hungrygeek/HSKB/case_customization/renders/hero2_sskb.png

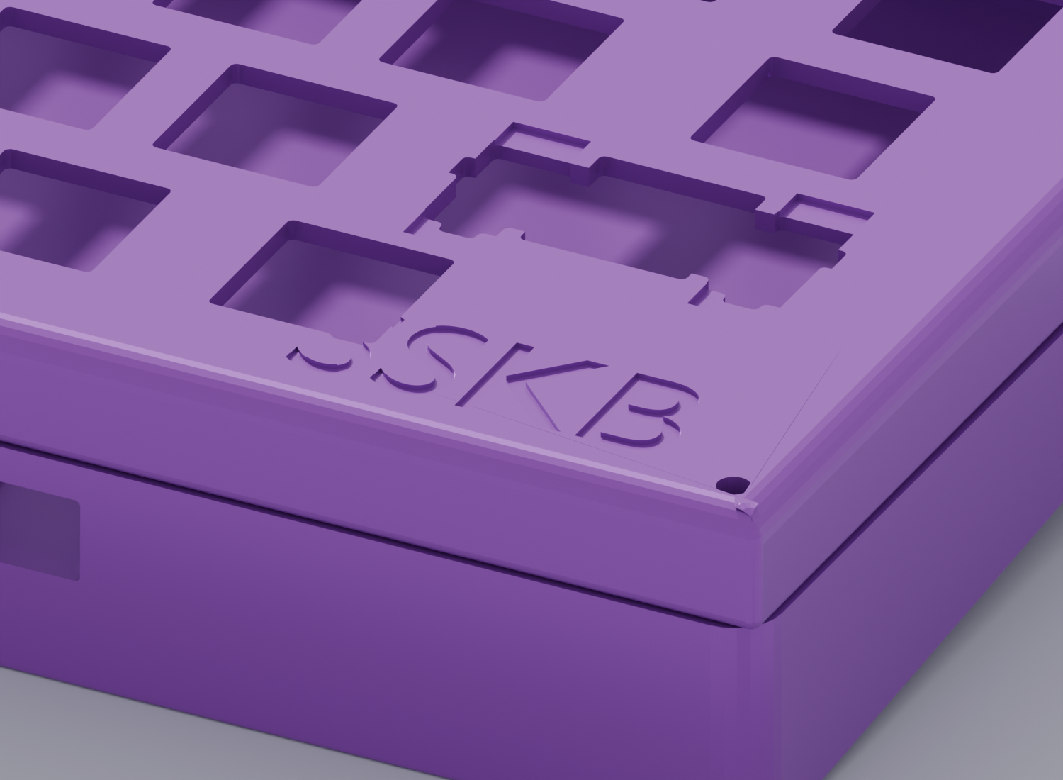
case_customization/renders/hero2_sskb.png
