hungrygeek/HSKB/case_customization/renders/hero3_sskb.png

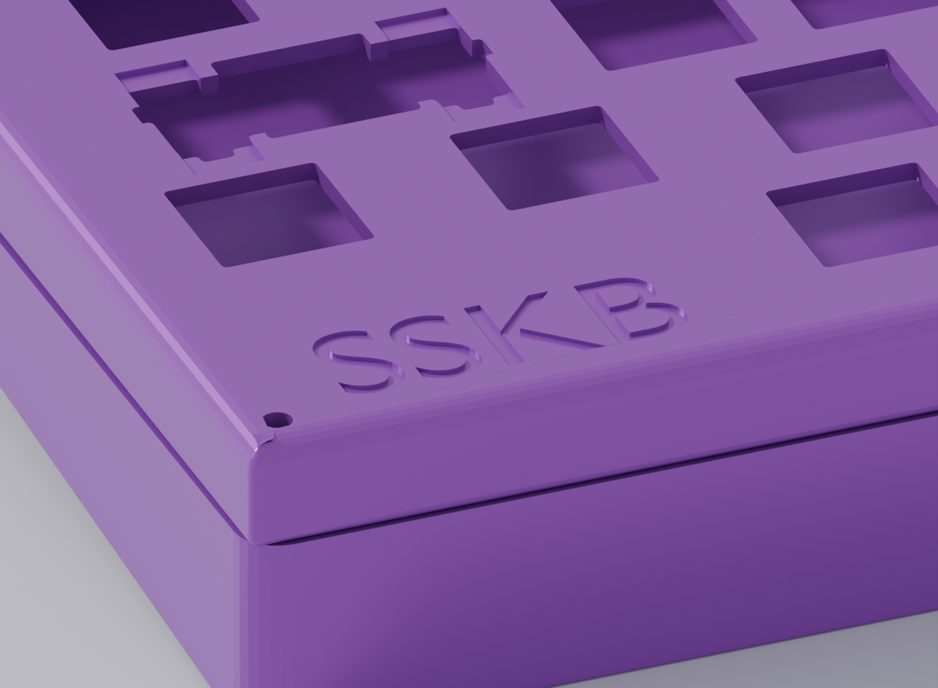
case_customization/renders/hero3_sskb.png
