hungrygeek/HSKB/case_customization/renders/after_15_corner.png

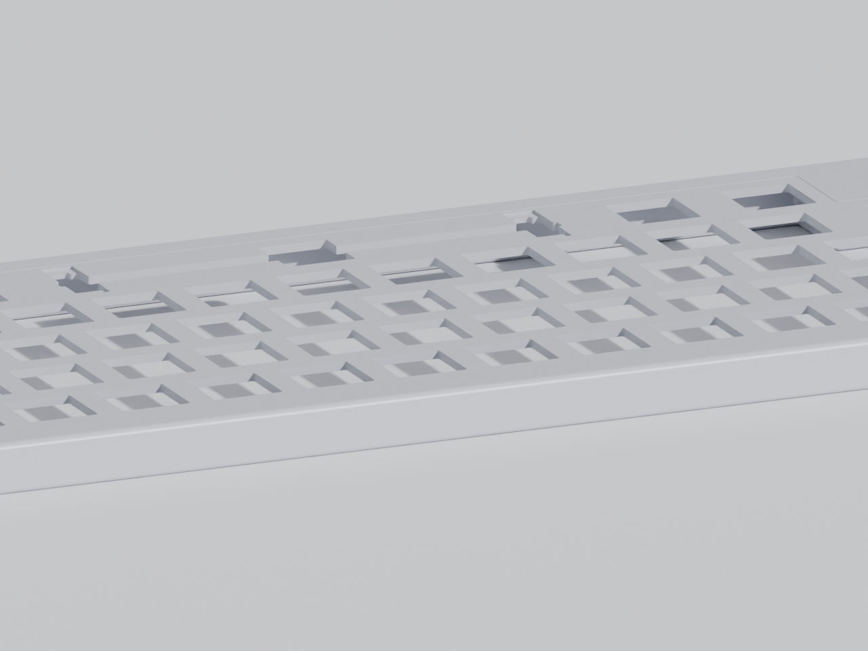
case_customization/renders/after_15_corner.png
