hungrygeek/HSKB/case_customization/renders/after_15_iso.png

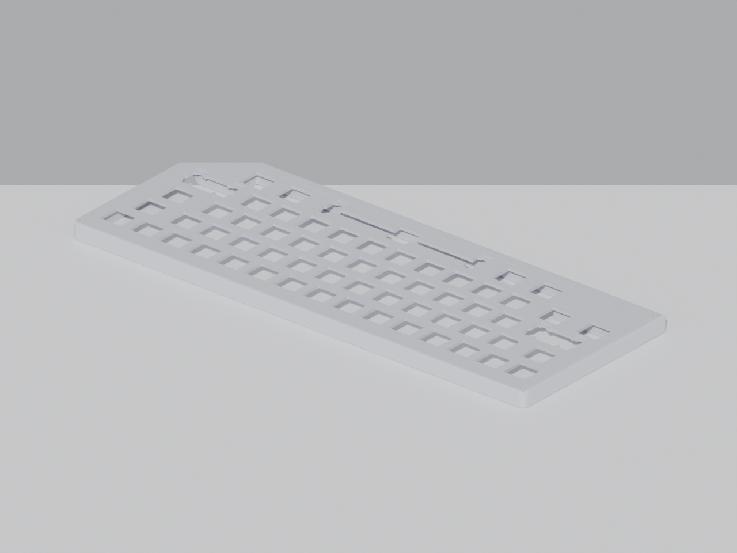
case_customization/renders/after_15_iso.png
