hungrygeek/HSKB/case_customization/renders/after_15_top.png

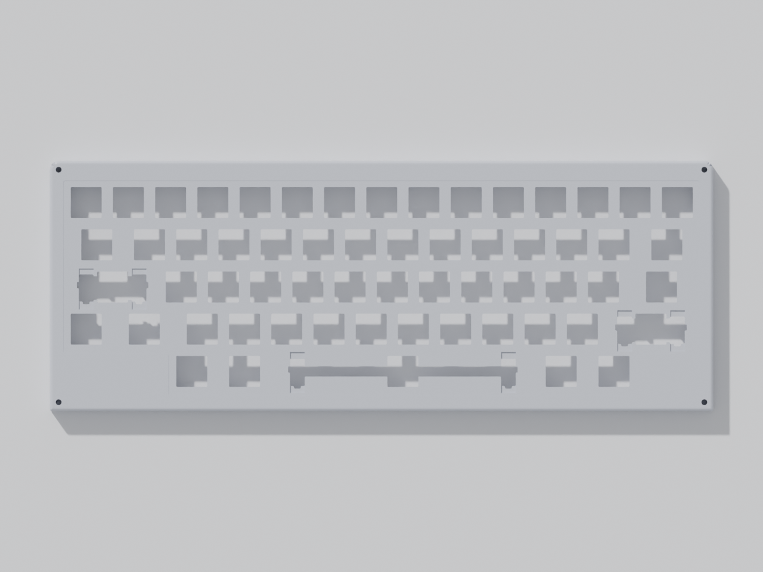
case_customization/renders/after_15_top.png
