hungrygeek/HSKB/case_customization/renders/bottom_before_corner.png

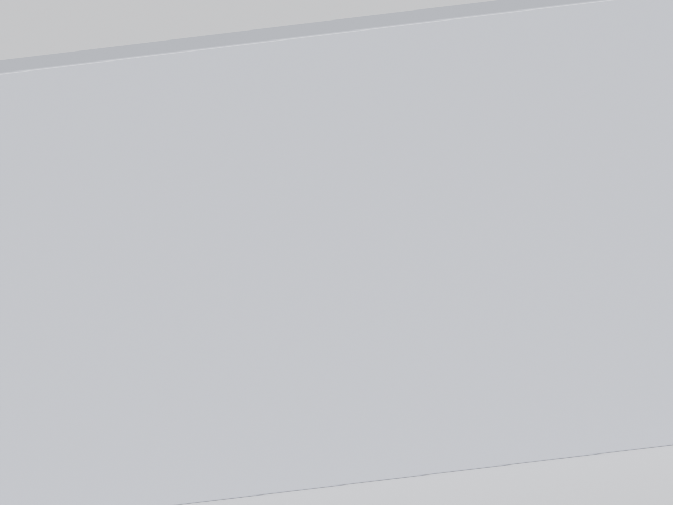
case_customization/renders/bottom_before_corner.png
