hungrygeek/HSKB/case_customization/renders/bottom_before_iso.png

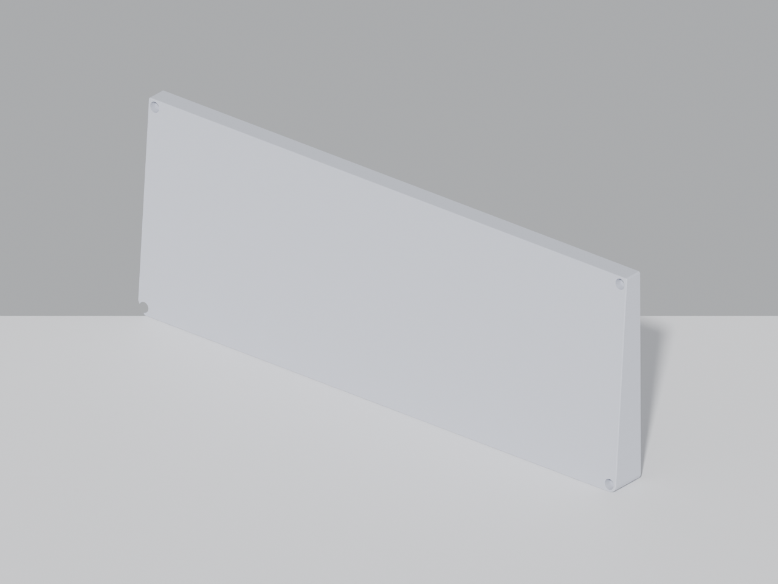
case_customization/renders/bottom_before_iso.png
