hungrygeek/HSKB/case_customization/renders/bottom_up_corner.png

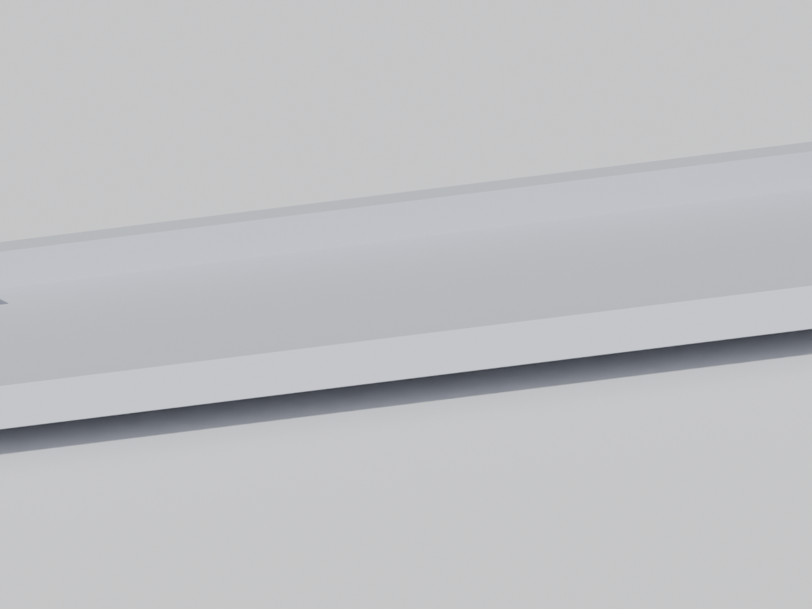
case_customization/renders/bottom_up_corner.png
