hungrygeek/HSKB/case_customization/renders/bottom_up_iso.png

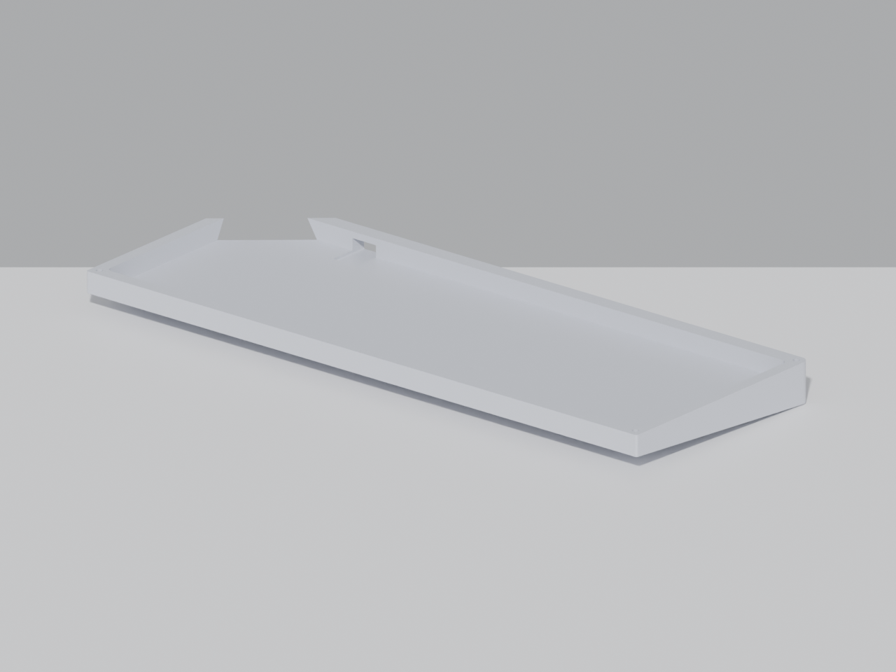
case_customization/renders/bottom_up_iso.png
