hungrygeek/HSKB/case_customization/renders/diag_frontright.png

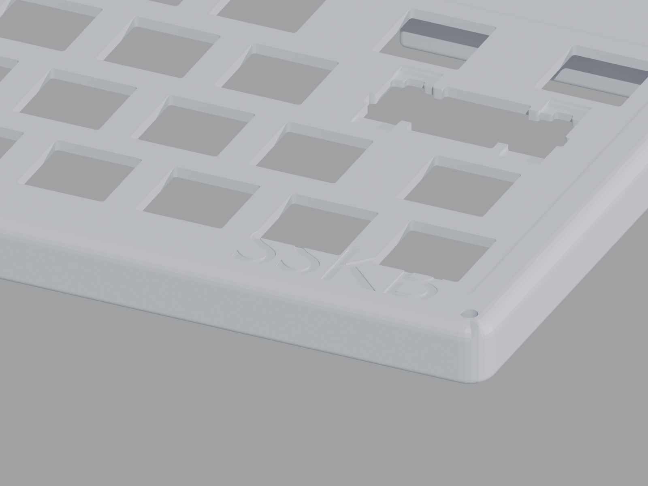
case_customization/renders/diag_frontright.png
