hungrygeek/HSKB/case_customization/renders/engrave2_angle.png

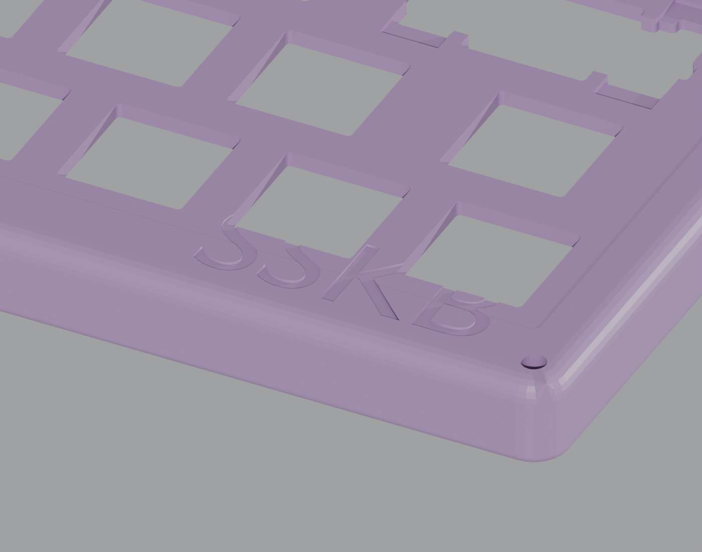
case_customization/renders/engrave2_angle.png
