hungrygeek/HSKB/case_customization/renders/engrave2_top.png

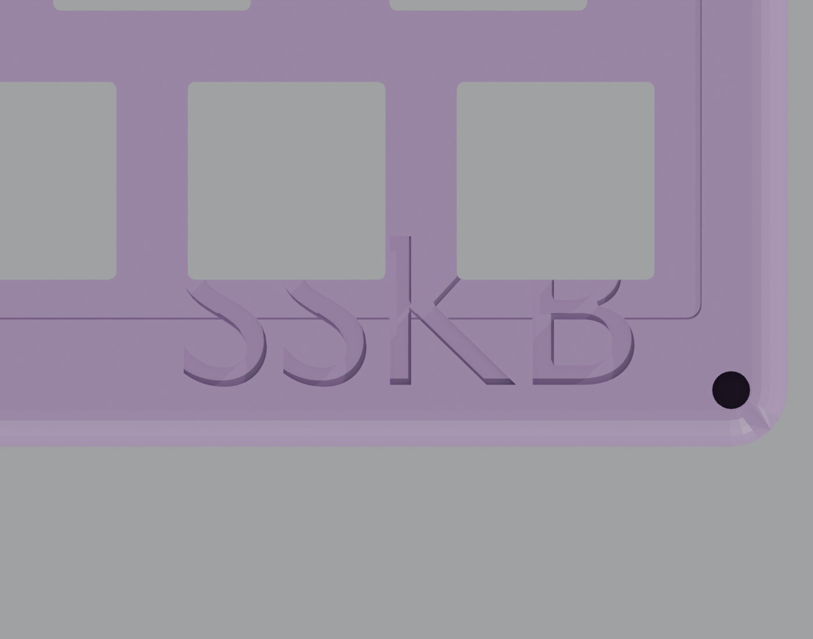
case_customization/renders/engrave2_top.png
