hungrygeek/HSKB/case_customization/renders/final_top_corner.png

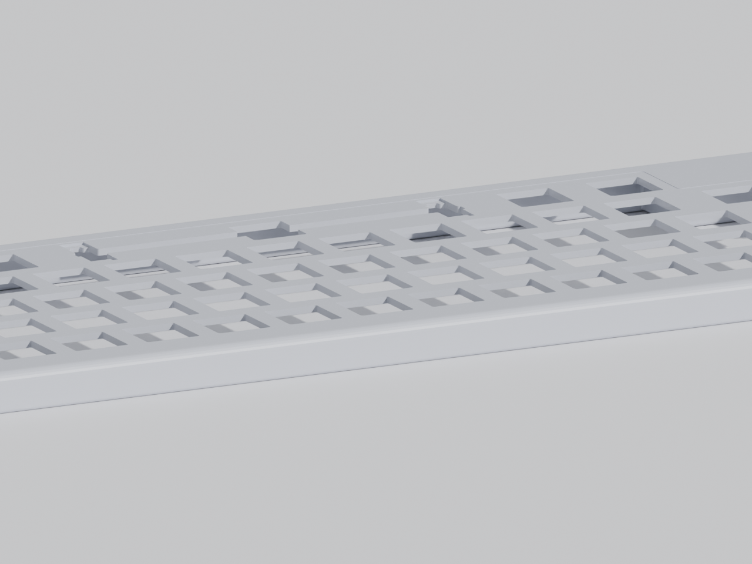
case_customization/renders/final_top_corner.png
