hungrygeek/HSKB/case_customization/renders/final_top_iso.png

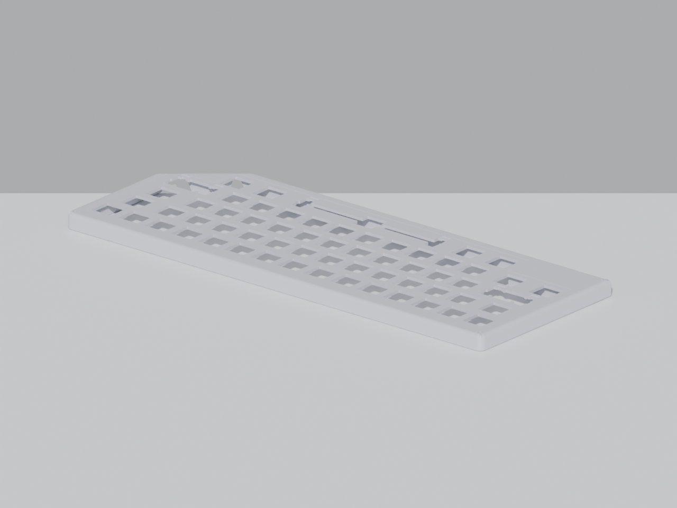
case_customization/renders/final_top_iso.png
