hungrygeek/HSKB/case_customization/renders/hero2_hero.png

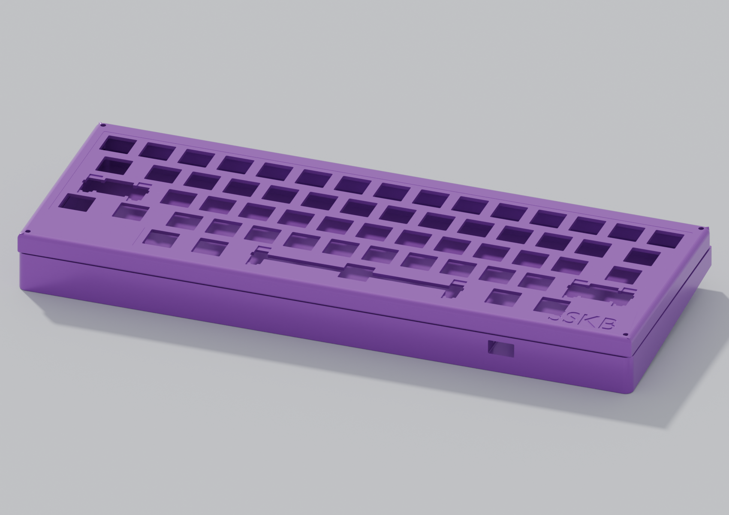
case_customization/renders/hero2_hero.png
