hungrygeek/HSKB/case_customization/renders/hero3_hero.png

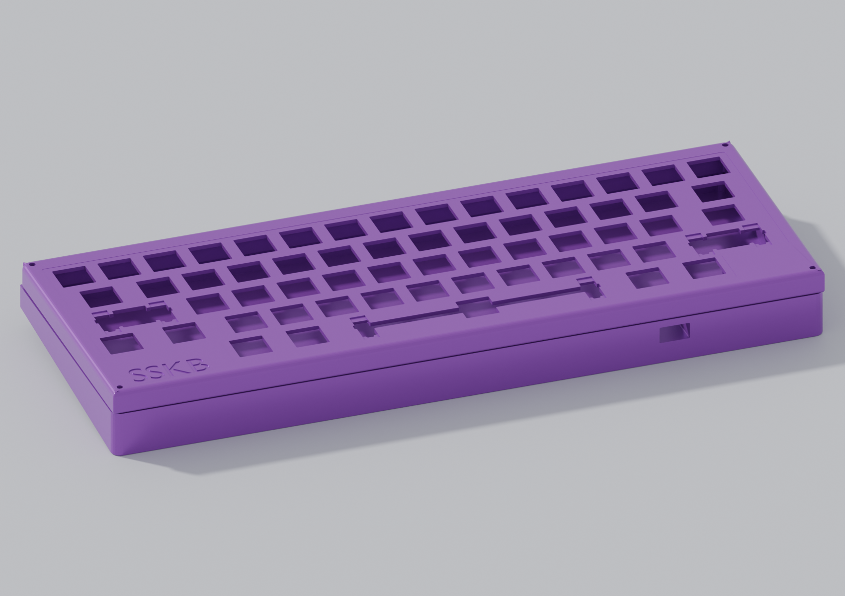
case_customization/renders/hero3_hero.png
