hungrygeek/HSKB/case_customization/renders/hero_hero.png

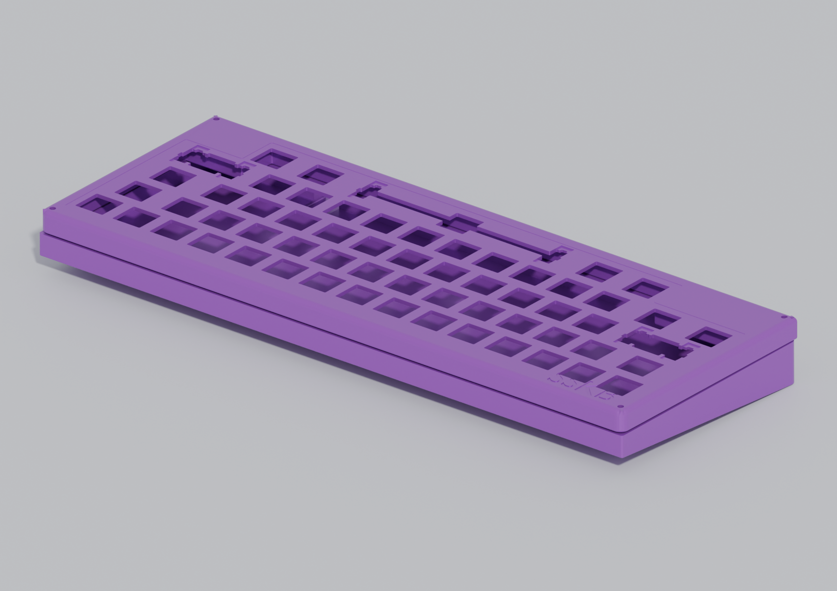
case_customization/renders/hero_hero.png
