hungrygeek/HSKB/case_customization/renders/hero_sskb.png

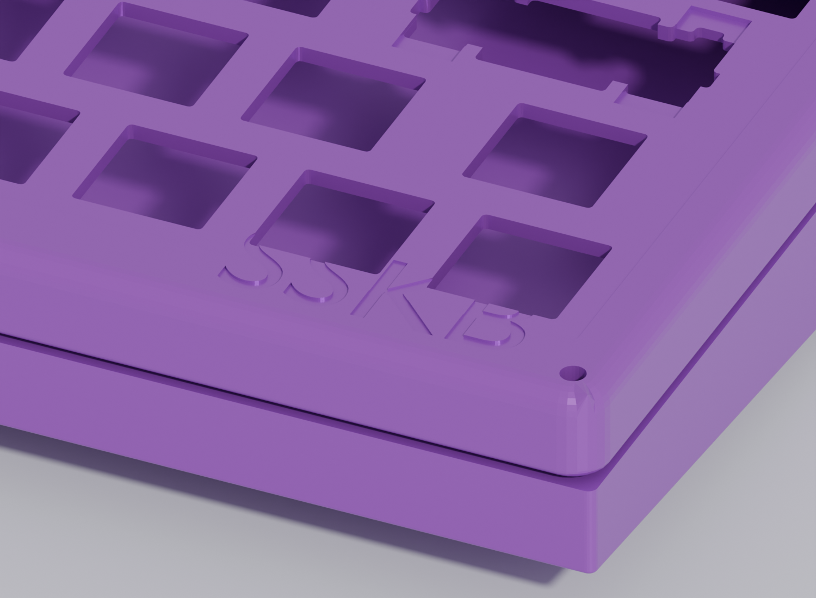
case_customization/renders/hero_sskb.png
