hungrygeek/HSKB/case_customization/renders/macro_sharp.png

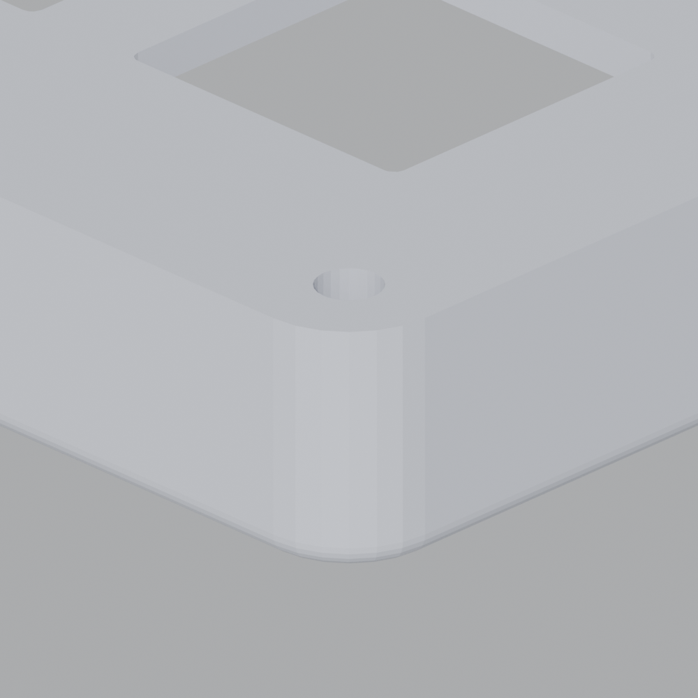
case_customization/renders/macro_sharp.png
