hungrygeek/HSKB/case_customization/renders/spacebar_iso.png

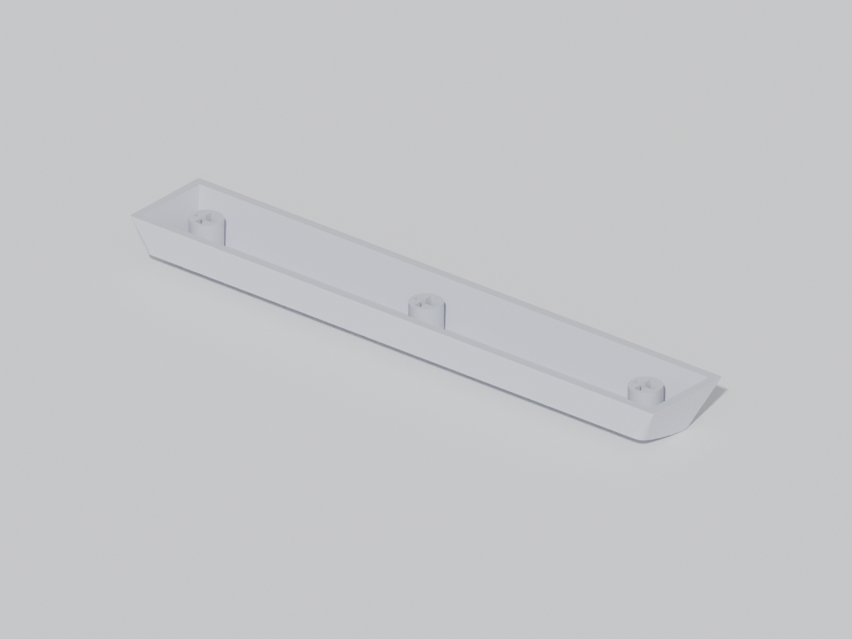
case_customization/renders/spacebar_iso.png
