hungrygeek/HSKB/case_customization/renders/spacebar_top.png

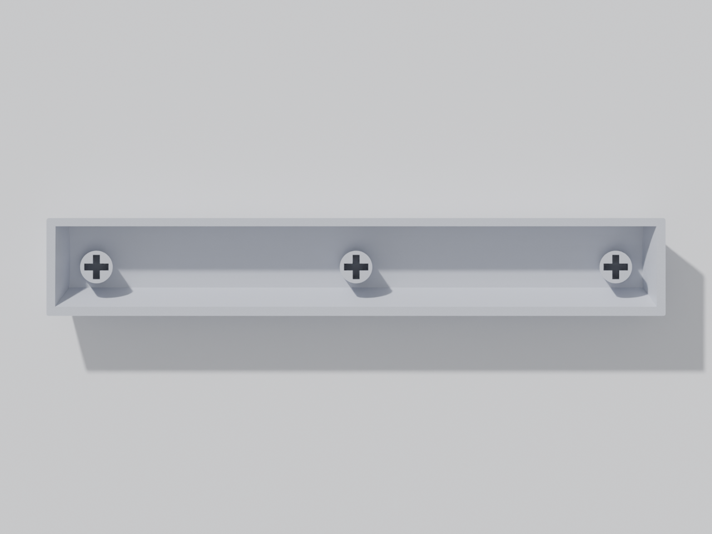
case_customization/renders/spacebar_top.png
