hungrygeek/HSKB/case_customization/renders/text_topdown.png

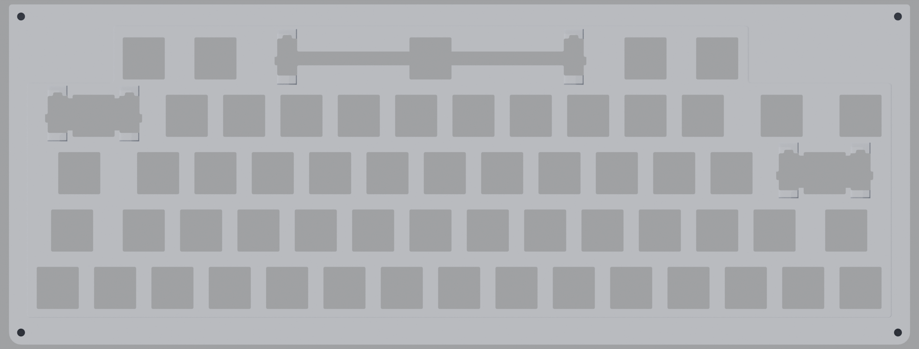
case_customization/renders/text_topdown.png
