hungrygeek/HSKB/case_customization/renders/fix1_front.png

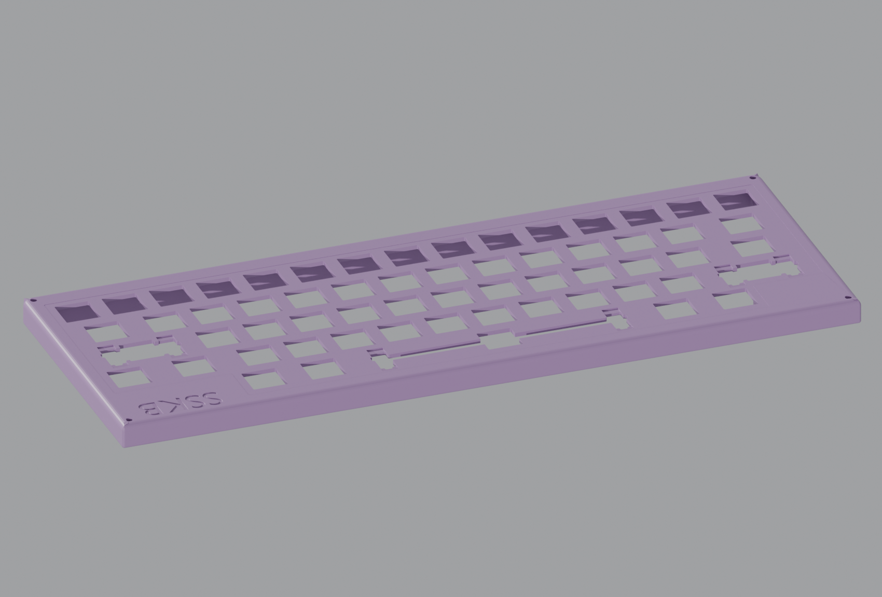
case_customization/renders/fix1_front.png
