hungrygeek/HSKB/case_customization/renders/fix1_top.png

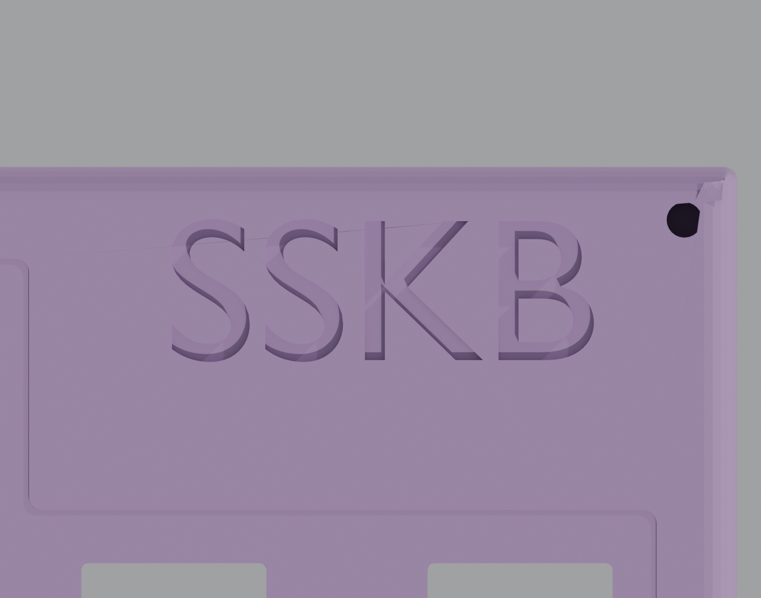
case_customization/renders/fix1_top.png
