hungrygeek/HSKB/case_customization/renders/fix2_front.png

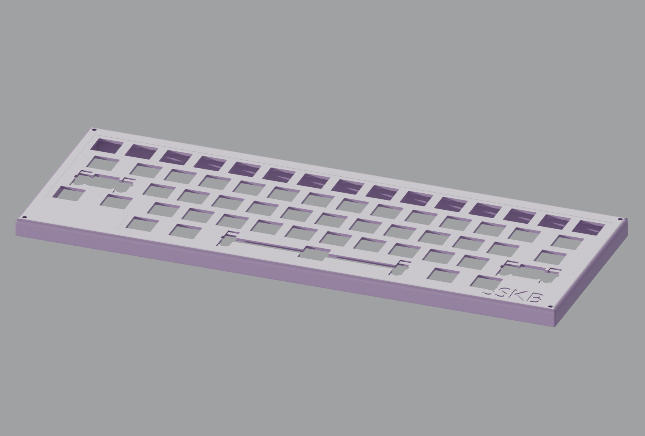
case_customization/renders/fix2_front.png
