hungrygeek/HSKB/case_customization/renders/fix2_top.png

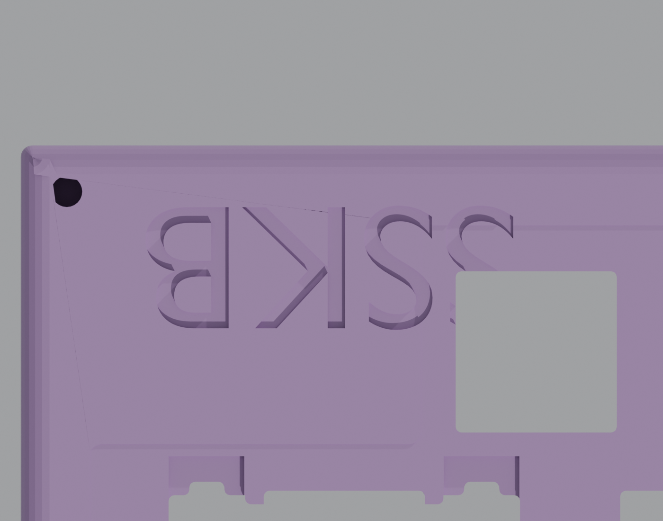
case_customization/renders/fix2_top.png
